MST6170/ADD2go/images/PXL_20260124_132410806.jpg

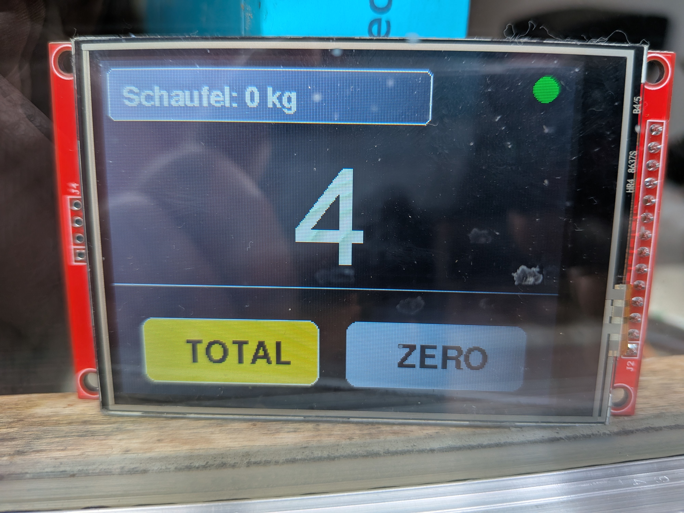
images/PXL_20260124_132410806.jpg
