MST6170/ADD2go/images/PXL_20260204_141707891.jpg

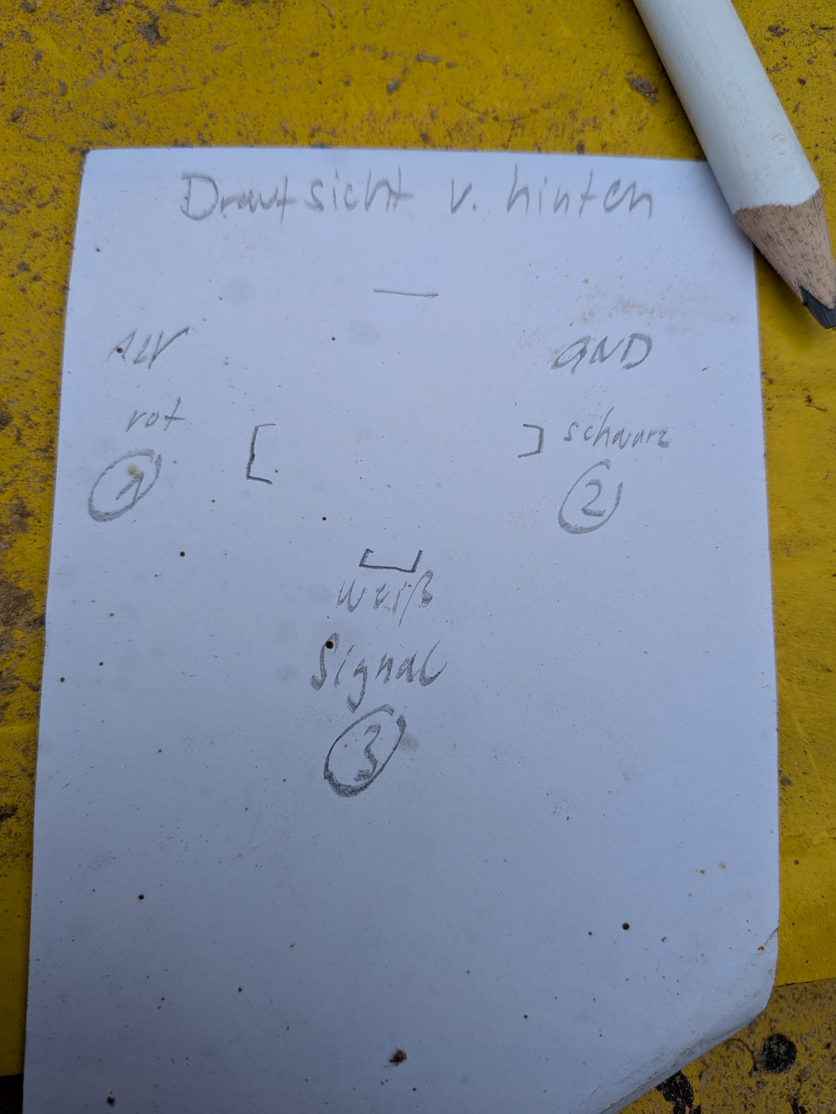
images/PXL_20260204_141707891.jpg
