MST6170/ADD2go/images/PXL_20260502_185309219.jpg

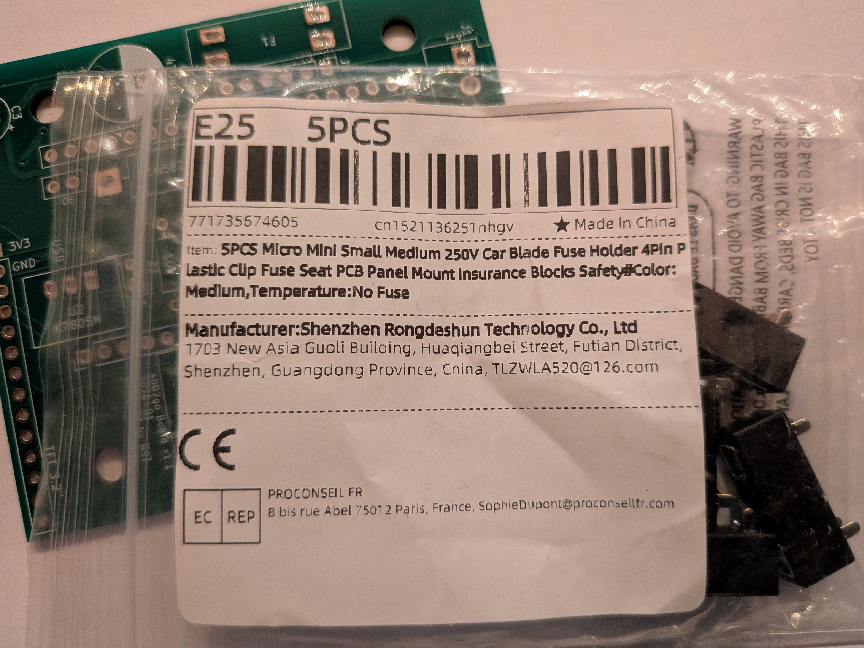
images/PXL_20260502_185309219.jpg
