MST6170/ADD2go/images/PXL_20260502_185325967.jpg

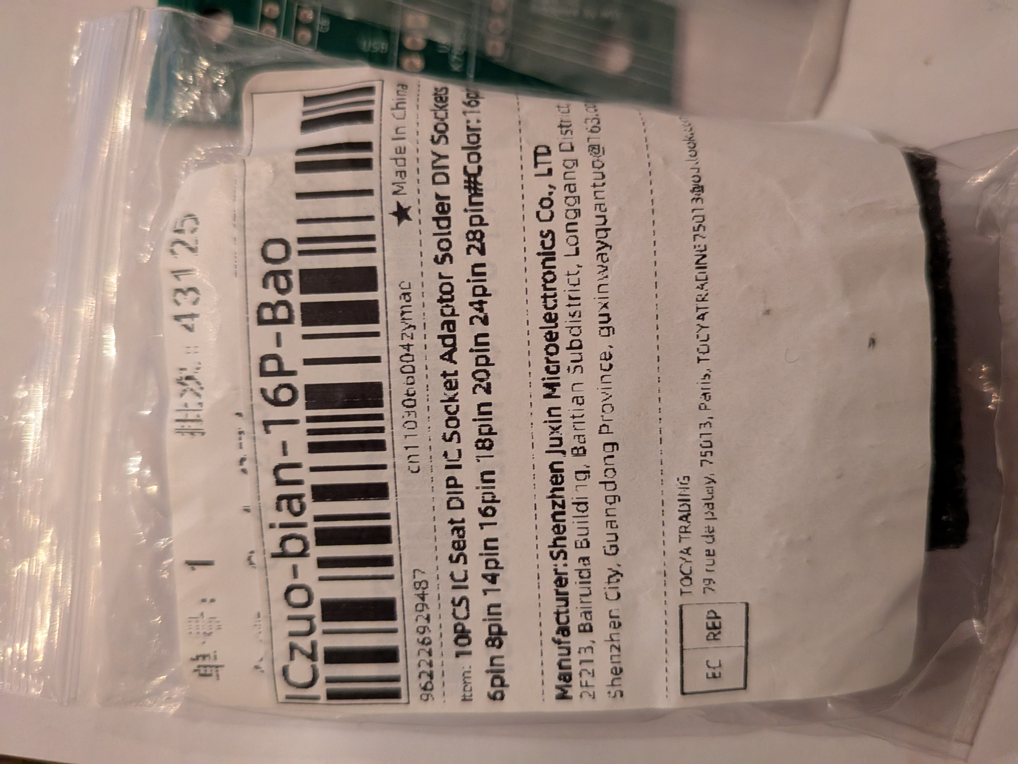
images/PXL_20260502_185325967.jpg
