MST6170/ADD2go/images/PXL_20260502_185809614.MP.jpg

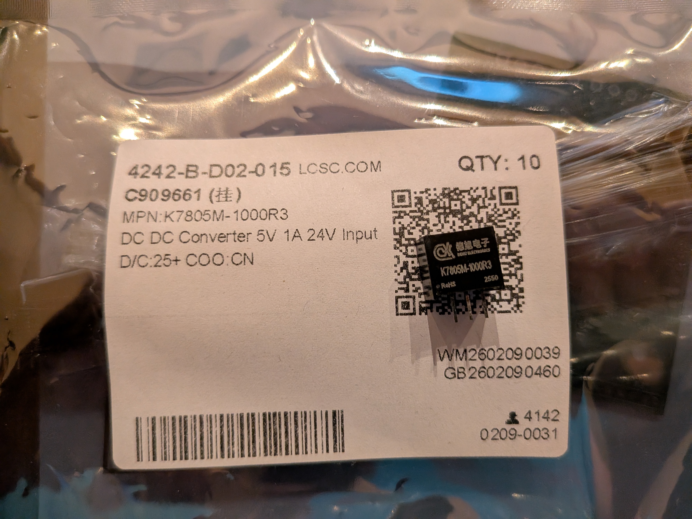
images/PXL_20260502_185809614.MP.jpg
