MST6170/ADD2go/images/PXL_20260502_190213237.jpg

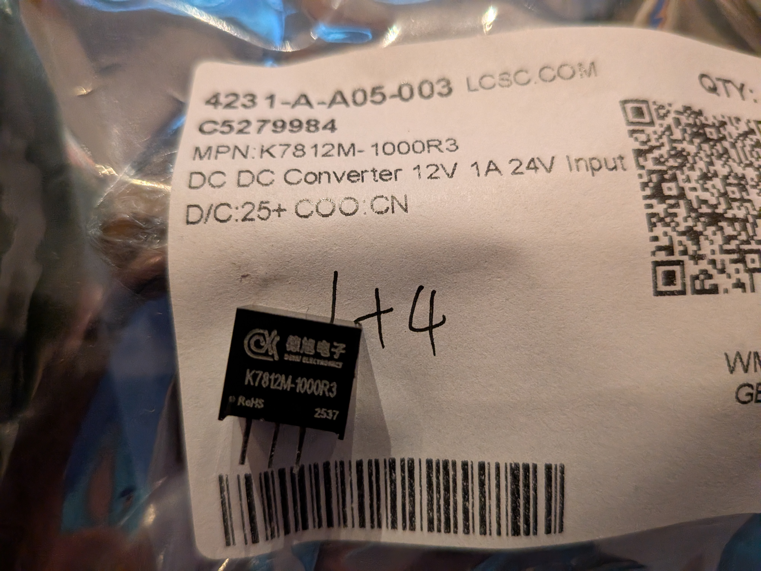
images/PXL_20260502_190213237.jpg
