MST6170/ADD2go/images/PXL_20260503_203123327.jpg

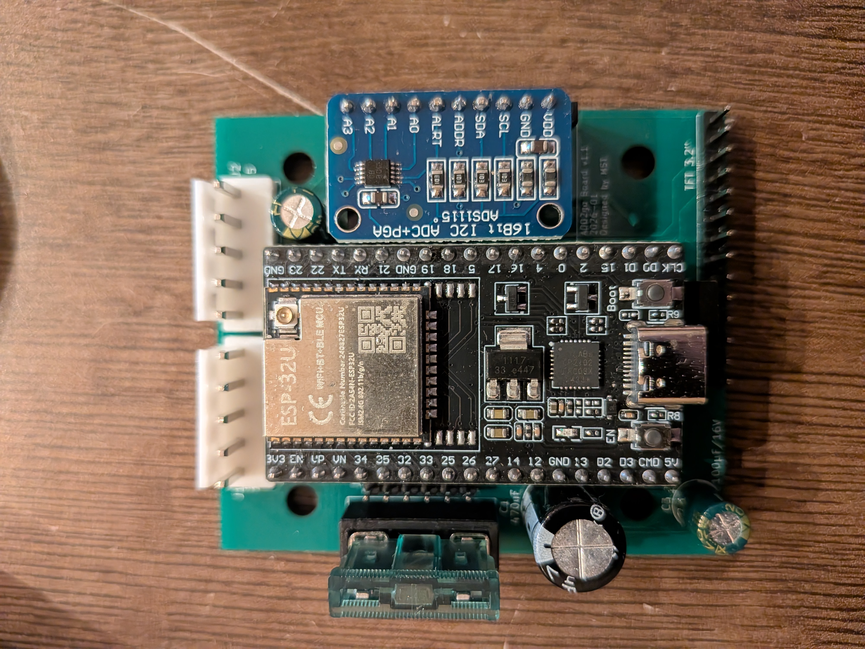
images/PXL_20260503_203123327.jpg
