MST6170/ADD2go/add2go_empfaenger_pio/src/ui.h

// UI Live-Update + Menue-Position-Tracking
// Migriert aus add2go_empfaenger_v1_0_2.ino Z. 598-616

#pragma once

namespace ui {

void handleMenuLiveUpdate();   // Detect Position-Wechsel im Menue, Force-Redraw

} // namespace ui
